Bitx86/z80-minimal-computer/files/minimal-z80-computer.kicad_sch

## KiCad design files/minimal-z80-computer.kicad_sch (2025-05-14)

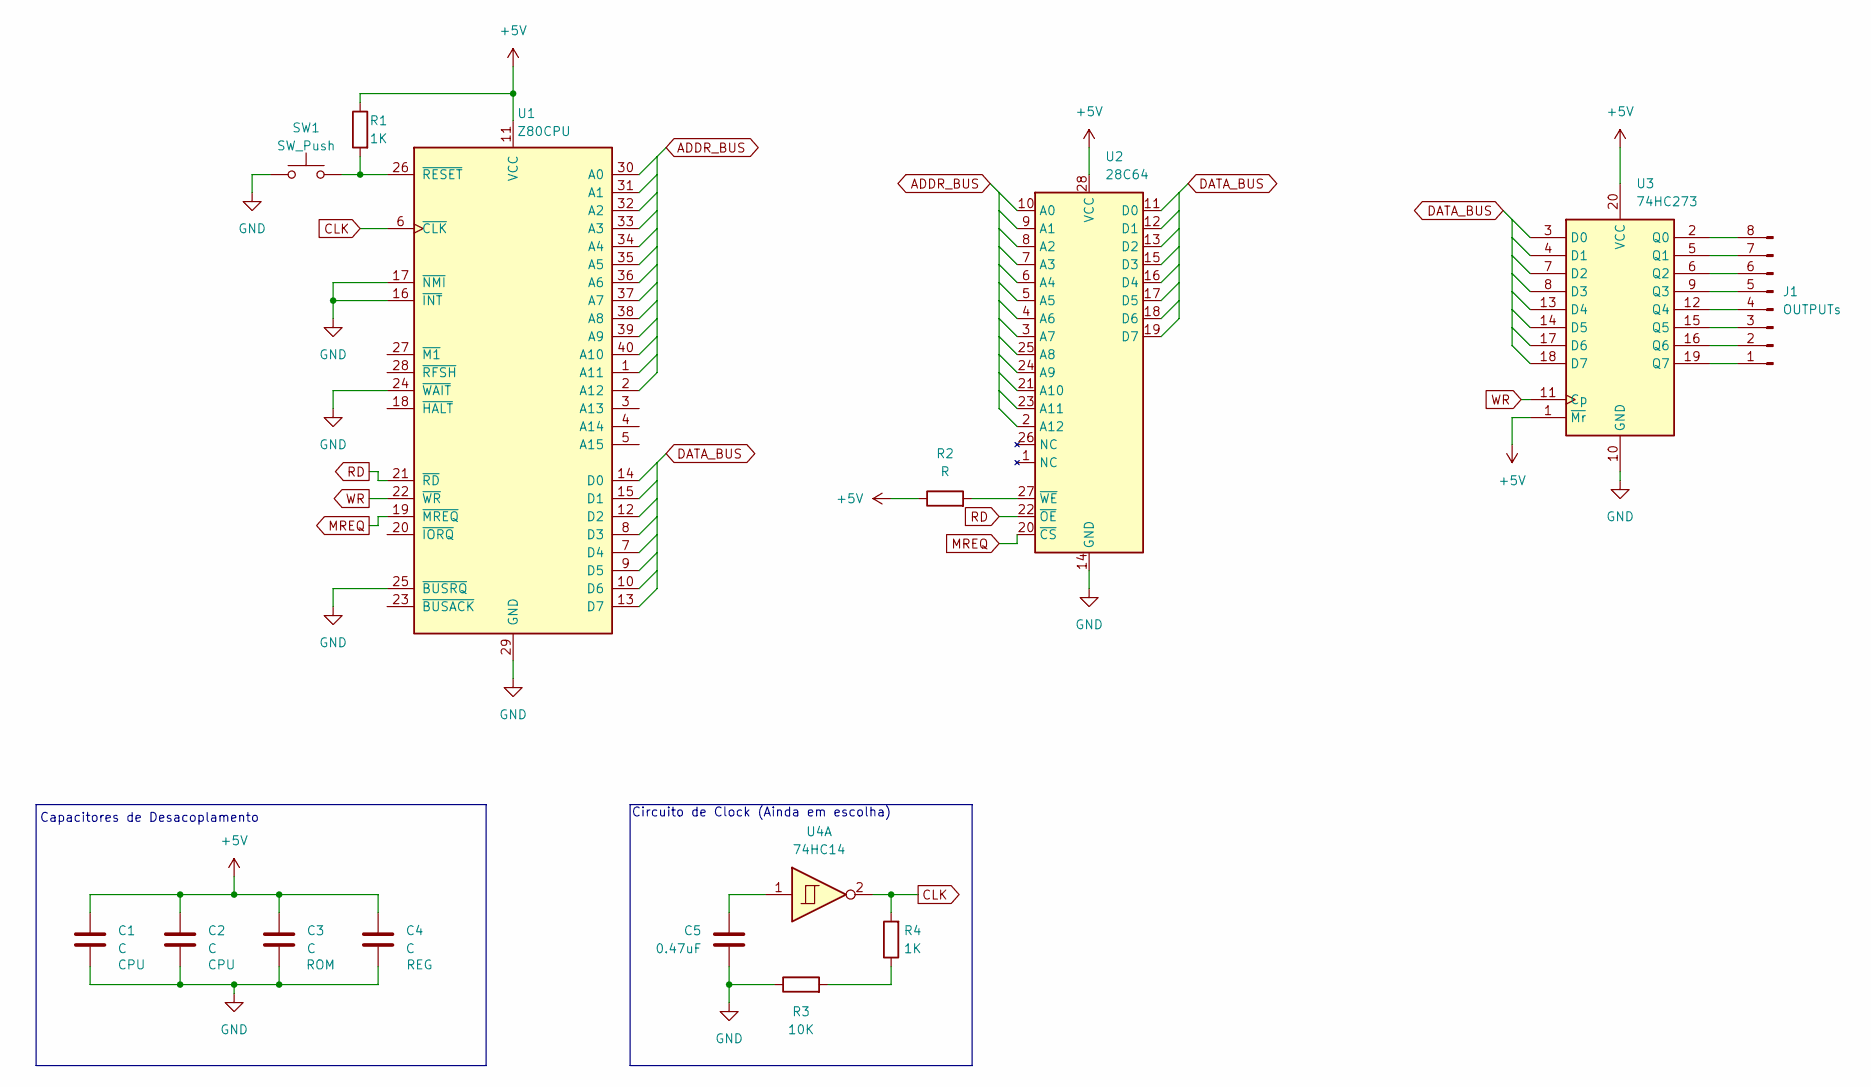
[picture p3: schematic minimal-z80-computer.kicad_sch]

Parts:
C1, C2, C3, C4: C
C5: 0.47uF
J1: OUTPUTs
R1, R4: 1K
R2: R
R3: 10K
SW1: SW_Push
U1: Z80CPU
U2: 28C64
U3: 74HC273
U4: 74HC14

Connections:
+5V: C1.1, C2.1, C3.1, C4.1, R1.1, R2.1, U1.11 (VCC), U2.28 (VCC), U3.1 (~Mr), U3.20 (VCC)
CLK: R4.2, U1.6 (~CLK), U4.2
GND: C1.2, C2.2, C3.2, C4.2, C5.1, R3.1, SW1.1, U1.16 (~INT), U1.17 (~NMI), U1.24 (~WAIT), U1.25 (~BUSRQ), U1.29 (GND), U2.14 (GND), U3.10 (GND)
MREQ: U1.19 (~MREQ), U2.20 (~CS)
unnamed: C5.2, U4.1
unnamed: J1.1, U3.19 (Q7)
unnamed: J1.2, U3.16 (Q6)
unnamed: J1.3, U3.15 (Q5)
unnamed: J1.4, U3.12 (Q4)
unnamed: J1.5, U3.9 (Q3)
unnamed: J1.6, U3.6 (Q2)
unnamed: J1.7, U3.5 (Q1)
unnamed: J1.8, U3.2 (Q0)
unnamed: R1.2, SW1.2, U1.26 (~RESET)
unnamed: R2.2, U2.27 (~WE)
unnamed: R3.2, R4.1
RD: U1.21 (~RD), U2.22 (~OE)
WR: U1.22 (~WR), U3.11 (Cp)

Notes on the sheet:
Circuito de Clock (Ainda em escolha)
Capacitores de Desacoplamento
